Faggenza/gigasound-midi/src/uart.c

#include "stdarg.h"
#include "string.h"
#include "main.h"
#include "stdio.h"

UART_HandleTypeDef huart1;

int printf(const char *format, ...)
{
    va_list args;
    va_start(args, format);
    char buffer[256];
    vsnprintf(buffer, sizeof(buffer), format, args);
    HAL_UART_Transmit(&huart1, (unsigned char *)buffer, strlen(buffer), 100);
    va_end(args);
    return strlen(buffer);
}

int puts(const char *str)
{
    HAL_UART_Transmit(&huart1, (unsigned char *)str, strlen(str), 100);
    return strlen(str);
}

void MX_USART1_UART_Init(void)
{
    huart1.Instance = USART1;
    huart1.Init.BaudRate = 115200;
    huart1.Init.WordLength = UART_WORDLENGTH_8B;
    huart1.Init.StopBits = UART_STOPBITS_1;
    huart1.Init.Parity = UART_PARITY_NONE;
    huart1.Init.Mode = UART_MODE_TX_RX;
    huart1.Init.HwFlowCtl = UART_HWCONTROL_NONE;
    huart1.Init.OverSampling = UART_OVERSAMPLING_16;
    if (HAL_UART_Init(&huart1) != HAL_OK)
    {
        Error_Handler();
    }
}
