Faggenza/gigasound-midi/include/calibrate.h

#ifndef CALIBRATE_H
#define CALIBRATE_H

#include <stdint.h>
#include "stdbool.h"

#define X_AXIS 10
#define Y_AXIS 9

typedef struct
{
    bool calibrated;
    uint16_t x_min;
    uint16_t x_max;
    uint16_t y_min;
    uint16_t y_max;
} joycon_calibration;

joycon_calibration calibrate_joycon(uint16_t *adc_buff);
#endif // CALIBRATE_H
