Faggenza/gigasound-midi/src/calibrate.c

#include "calibrate.h"
#include "input.h"

joycon_calibration calibrate_joycon(uint16_t *adc_buff)
{
    joycon_calibration cal = {
        .calibrated = true,
        .x_min = 4095,
        .x_max = 0,
        .y_min = 4095,
        .y_max = 0};

    while (!was_key_pressed(STOP))
    {
        // TODO: add loop_task() here to avoid problems with usb
        if (adc_complete)
        {
            adc_complete = 0;
            if (adc_buff[10] < cal.x_min)
                cal.x_min = adc_buff[10];
            if (adc_buff[10] > cal.x_max)
                cal.x_max = adc_buff[10];
            if (adc_buff[9] < cal.y_min)
                cal.y_min = adc_buff[9];
            if (adc_buff[9] > cal.y_max)
                cal.y_max = adc_buff[9];
        }
    }
    return cal;
}
